FaisalHussain95/esp32-espnow-led-spots/wifi_bridge_firmware/src/config.h

#pragma once

// ─── WiFi + MQTT credentials (set via: pio run --target menuconfig) ───────────
#define WIFI_SSID        CONFIG_WIFI_SSID
#define WIFI_PASSWORD    CONFIG_WIFI_PASSWORD
#define MQTT_BROKER_IP   CONFIG_MQTT_BROKER_IP
#define MQTT_PORT        CONFIG_MQTT_PORT
#define MQTT_USER        CONFIG_MQTT_USER
#define MQTT_PASSWORD    CONFIG_MQTT_PASSWORD

// ─── UART1 pins (connect to Master ESP32-C3) ──────────────────────────────────
// Bridge GPIO6 TX → Master GPIO7 RX
// Bridge GPIO7 RX ← Master GPIO6 TX
#define PIN_UART1_TX  6
#define PIN_UART1_RX  7

// ─── MQTT topic prefix ────────────────────────────────────────────────────────
// Command:  homeassistant/led_spots/<id>/set    (subscribed)
// State:    homeassistant/led_spots/<id>/state  (published)
// Discovery: homeassistant/light/led_spot_<id>/config
#define MQTT_TOPIC_PREFIX  "homeassistant/led_spots"
#define MQTT_CLIENT_ID     "led-spots-bridge"
#define NUM_SPOTS          13

// ─── Firmware Version ─────────────────────────────────────────────────────────
#define FW_VERSION  31

// ─── UART2 frame bytes (must match master_firmware) ───────────────────────────
#define UART2_START    0xAA
#define UART2_END      0x55
#define UART2_CMD      0x01
#define UART2_STATUS   0x02
#define UART2_VERSION  0x03

// ─── ESP-NOW command codes (must match spot_firmware/config.h) ────────────────
#define CMD_SET_BRIGHTNESS  0x01
#define CMD_TURN_ON         0x02
#define CMD_TURN_OFF        0x03
#define CMD_REQUEST_STATUS  0x04

// ─── Thermal states ───────────────────────────────────────────────────────────
#define THERMAL_NORMAL    0
#define THERMAL_THROTTLE  1
#define THERMAL_CRITICAL  2
